yasaspeiris/WKnight-SLRC2018/Parts/midgear.STL

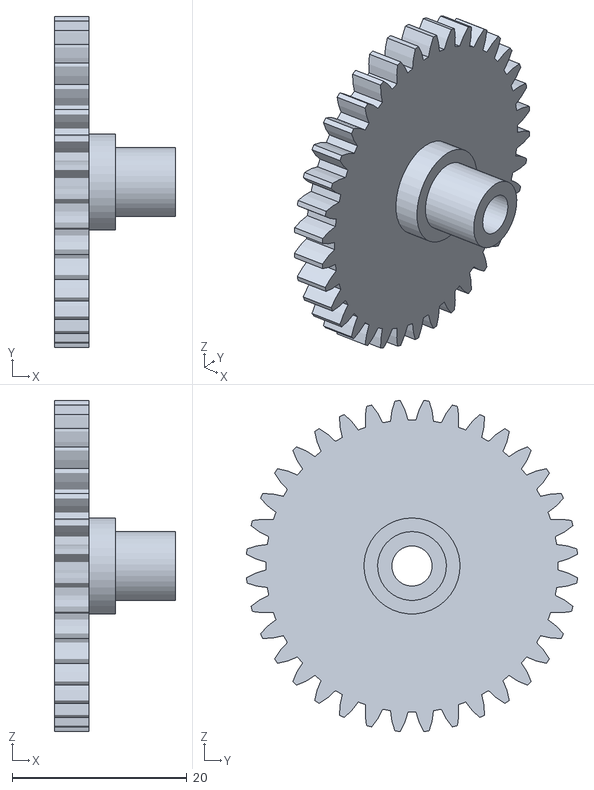
[picture p16: CAD file, 2019-01-25]
Parts/midgear.STL
13.9 x 37.9 x 37.9
