yasaspeiris/WKnight-SLRC2018/Parts/rack1.STL

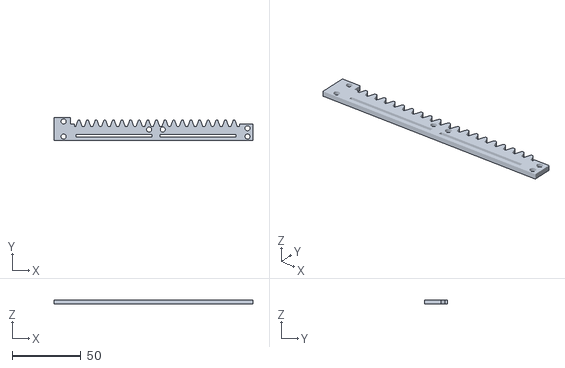
[picture p17: CAD file, 2019-01-25]
Parts/rack1.STL
145.0 x 17.0 x 3.00
