yasaspeiris/WKnight-SLRC2018/Parts/batterymount.STL

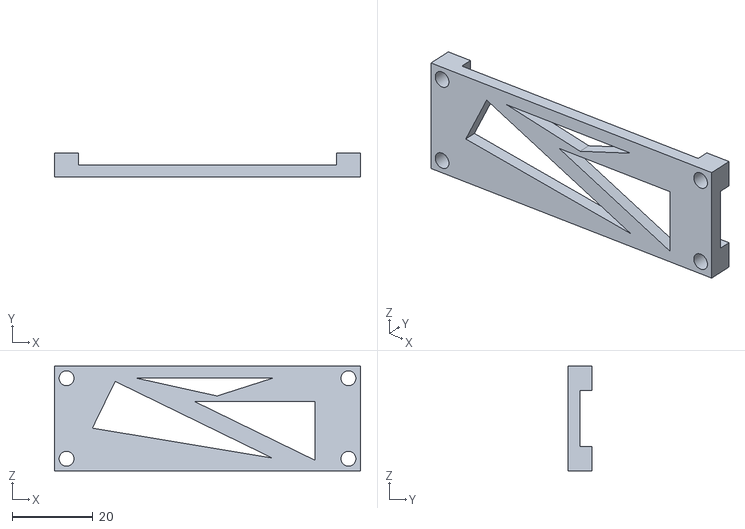
[picture p18: CAD file, 2019-01-25]
Parts/batterymount.STL
76.0 x 6.00 x 26.0
