yasaspeiris/WKnight-SLRC2018/Parts/bearingspacer_new_2.STL

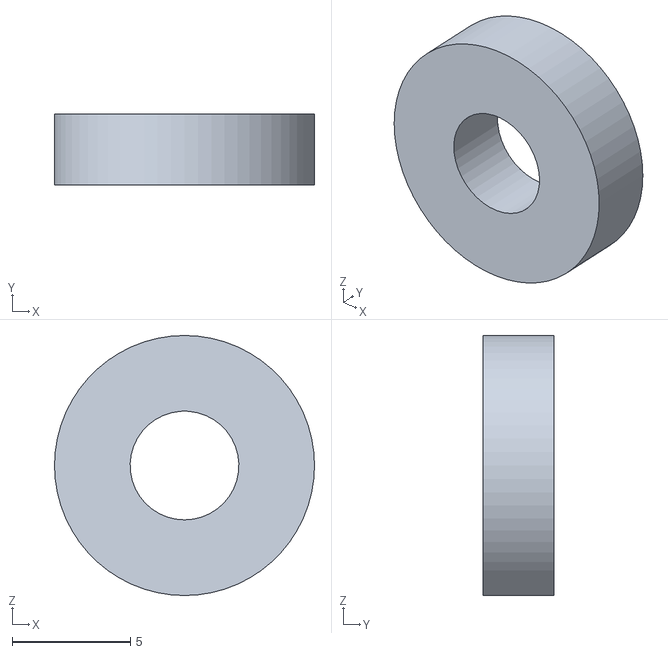
[picture p19: CAD file, 2019-01-25]
Parts/bearingspacer_new_2.STL
11.0 x 3.00 x 11.0
