yasaspeiris/WKnight-SLRC2018/Parts/trayeject.STL

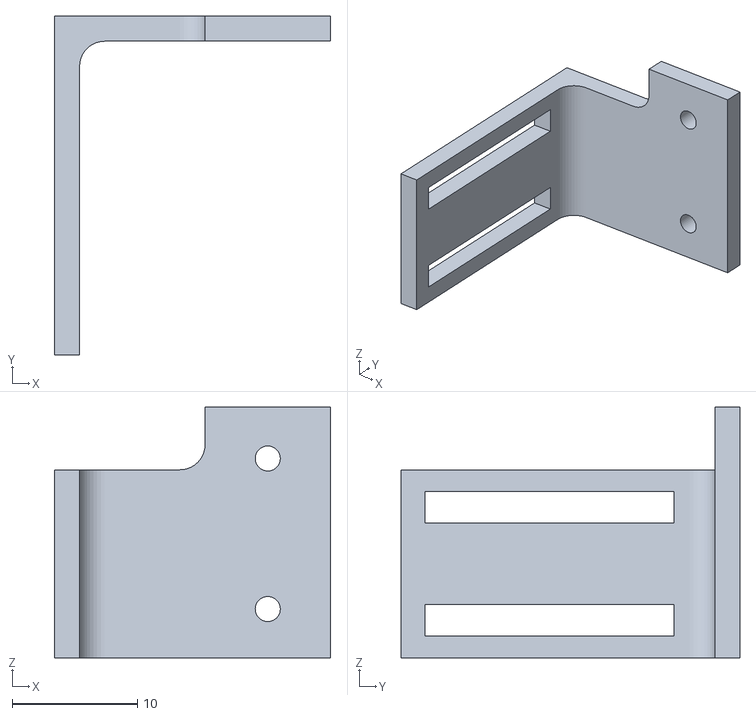
[picture p20: CAD file, 2019-01-25]
Parts/trayeject.STL
22.0 x 27.0 x 20.0
