yasaspeiris/WKnight-SLRC2018/Parts/wheelgear.STL

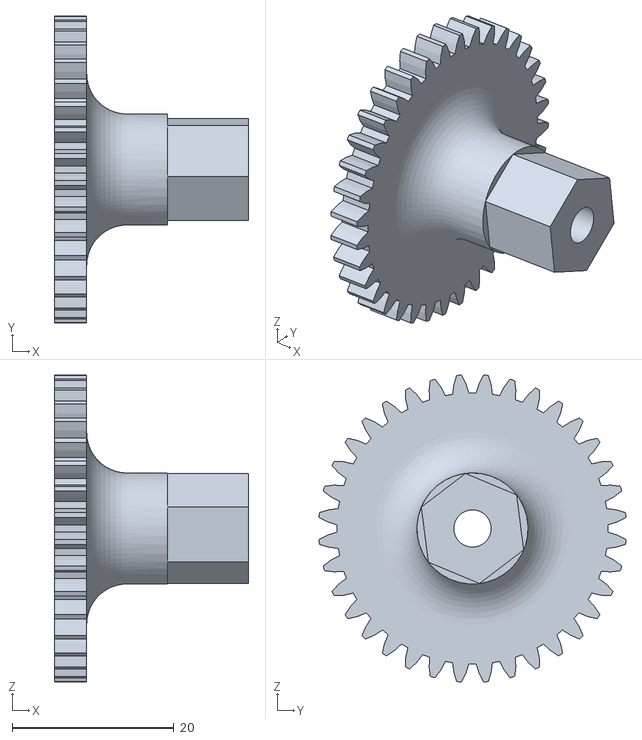
[picture p21: CAD file, 2019-01-25]
Parts/wheelgear.STL
24.0 x 37.9 x 37.9
