yasaspeiris/WKnight-SLRC2018/Parts/rightsidewall.STL

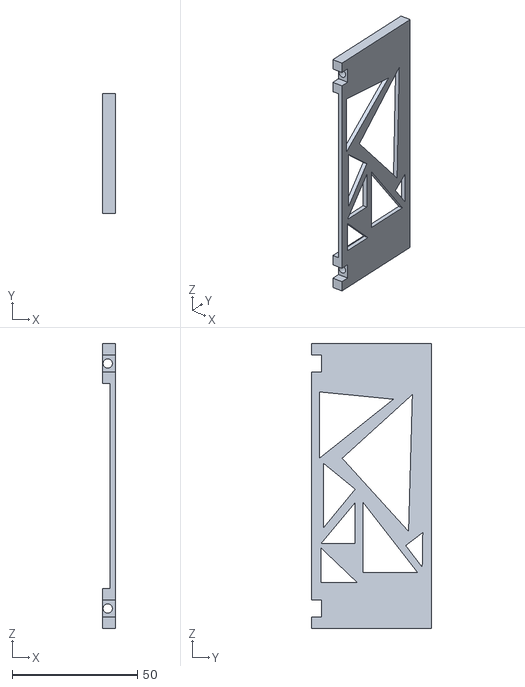
[picture p22: CAD file, 2019-01-25]
Parts/rightsidewall.STL
5.00 x 48.0 x 114.0
