yasaspeiris/WKnight-SLRC2018/Parts/experimental_motorgear.STL

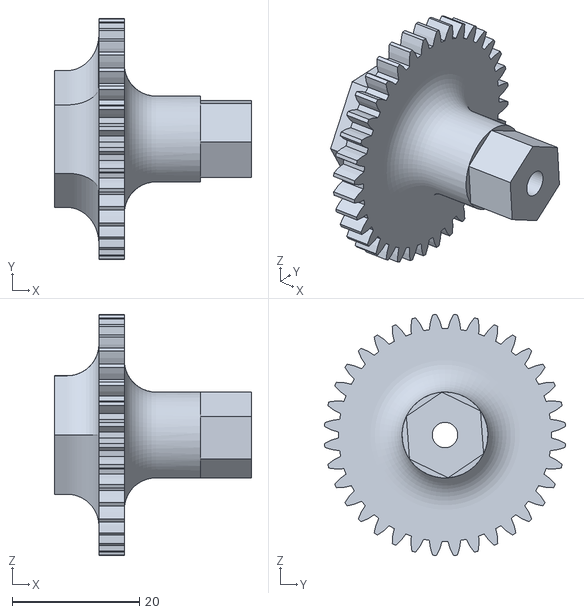
[picture p23: CAD file, 2019-01-25]
Parts/experimental_motorgear.STL
31.0 x 37.9 x 37.9
