yasaspeiris/WKnight-SLRC2018/Parts/base_top1-newnew.STL

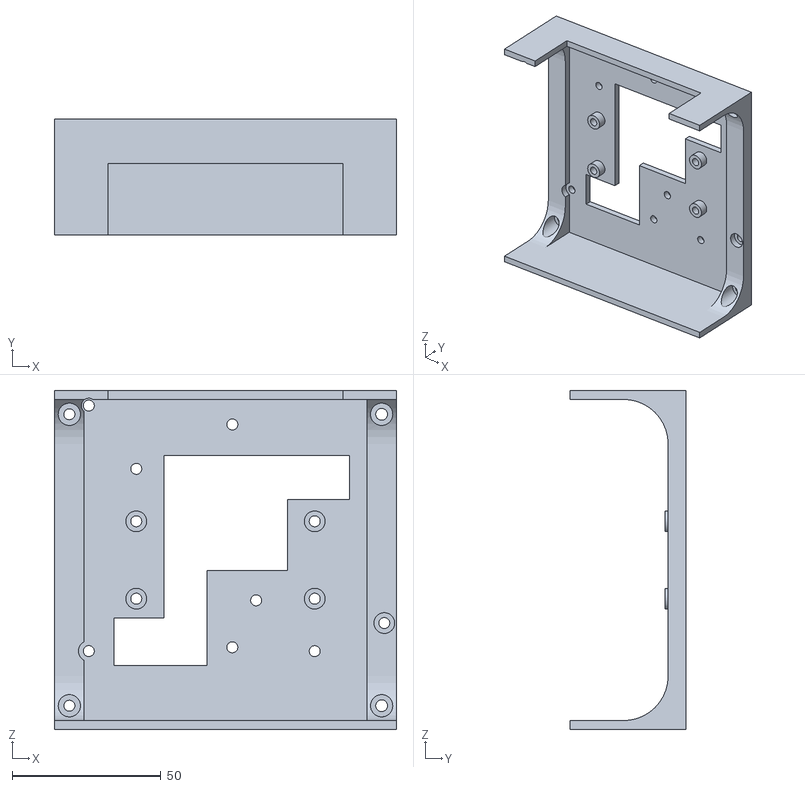
[picture p24: CAD file, 2019-01-25]
Parts/base_top1-newnew.STL
115.0 x 39.0 x 114.0
