yasaspeiris/WKnight-SLRC2018/Parts/coinremover.STL

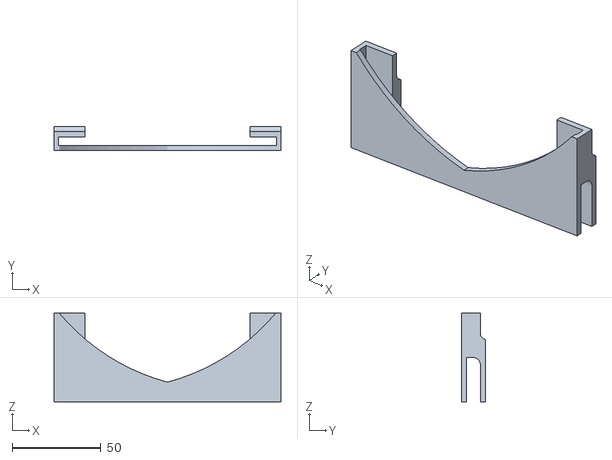
[picture p25: CAD file, 2019-01-25]
Parts/coinremover.STL
128.0 x 13.7 x 50.0
