yasaspeiris/WKnight-SLRC2018/Parts/qtrcholder_sub.STL

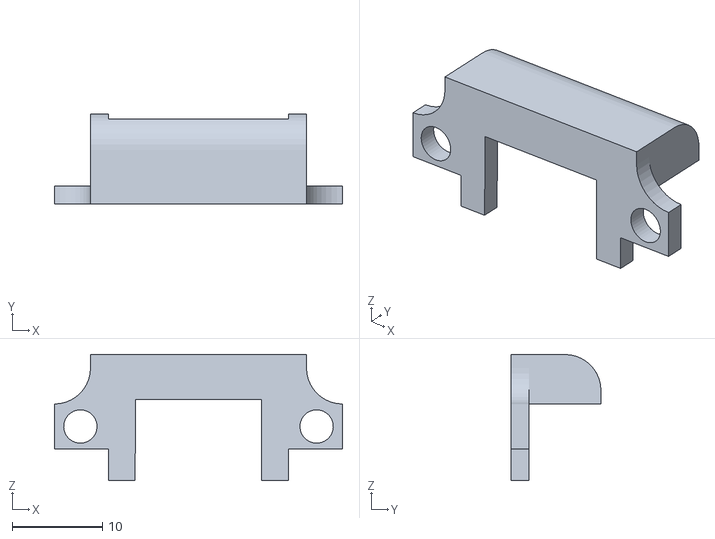
[picture p26: CAD file, 2019-01-25]
Parts/qtrcholder_sub.STL
32.0 x 10.0 x 14.0
