yasaspeiris/WKnight-SLRC2018/Parts/spurgear.STL

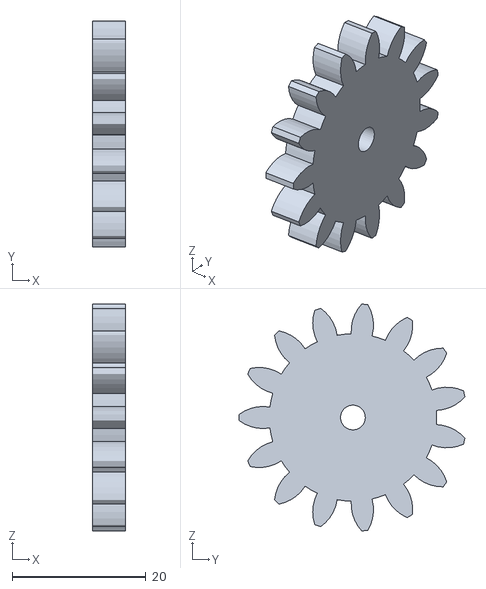
[picture p27: CAD file, 2019-01-25]
Parts/spurgear.STL
5.00 x 33.7 x 33.9
