yasaspeiris/WKnight-SLRC2018/Parts/base.STL

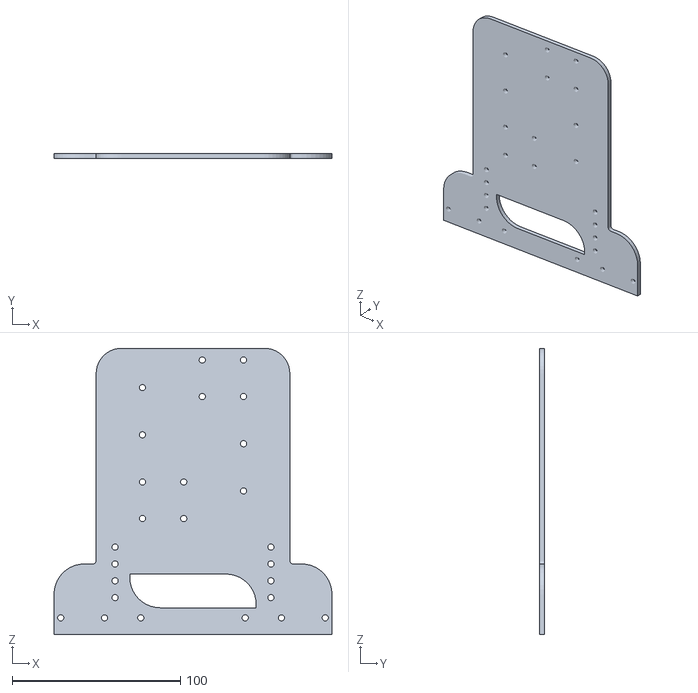
[picture p28: CAD file, 2019-01-25]
Parts/base.STL
165.0 x 3.00 x 170.0
