yasaspeiris/WKnight-SLRC2018/Parts/compartment.STL

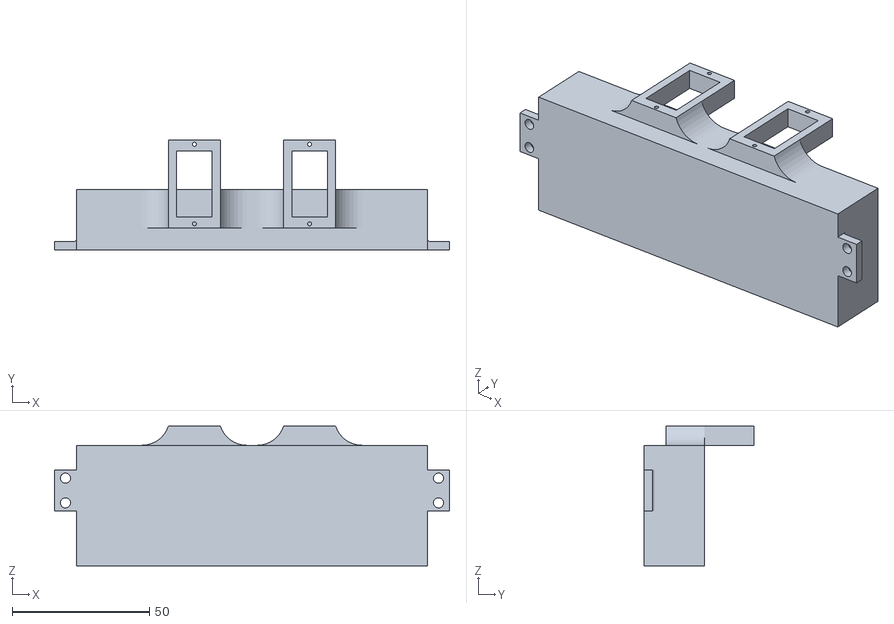
[picture p29: CAD file, 2019-01-25]
Parts/compartment.STL
144.0 x 40.0 x 51.0
