yasaspeiris/WKnight-SLRC2018/Parts/compcover1.STL

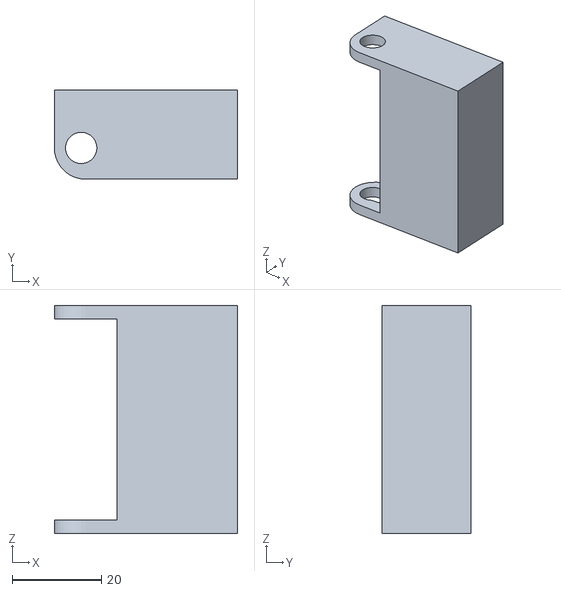
[picture p30: CAD file, 2019-01-25]
Parts/compcover1.STL
41.0 x 20.0 x 51.0
