yasaspeiris/WKnight-SLRC2018/Parts/spurgear2.STL

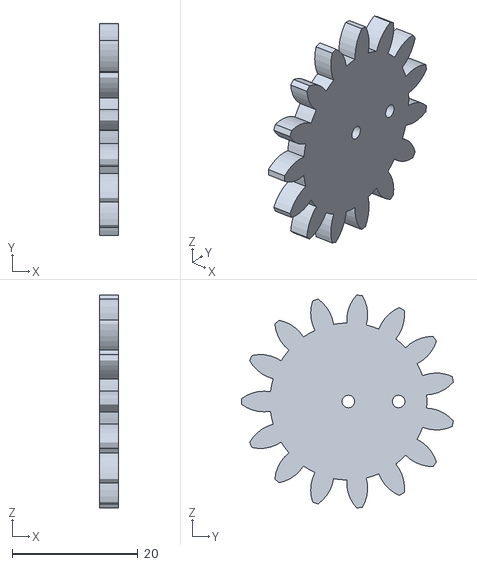
[picture p31: CAD file, 2019-01-25]
Parts/spurgear2.STL
3.00 x 33.7 x 33.9
