yasaspeiris/WKnight-SLRC2018/Parts/spacer.STL

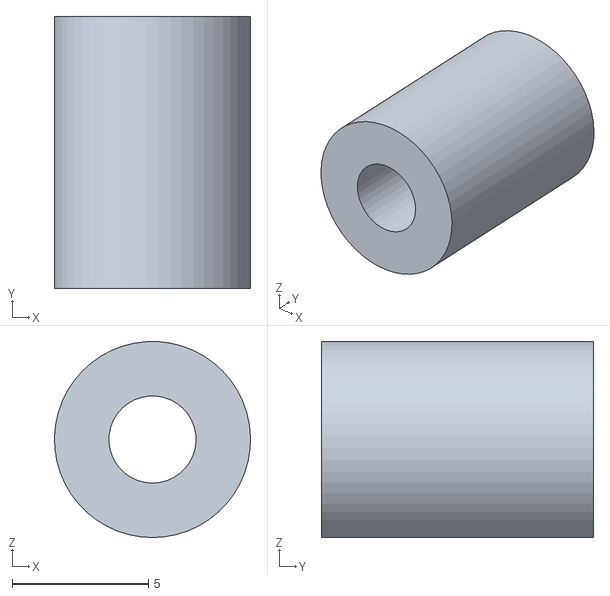
[picture p32: CAD file, 2019-01-25]
Parts/spacer.STL
7.20 x 10.0 x 7.20
