yasaspeiris/WKnight-SLRC2018/SLRC2019/lightsandsw.ino

void lightsandswsetup() {
  pinMode(STARTSWITCH, INPUT);
  pinMode(MODESW, INPUT);
  pinMode(CALSW,INPUT);
  pinMode(GREENLED,OUTPUT);
  pinMode(BLUELED, OUTPUT);
  pinMode(YELLOWLED, OUTPUT);
  

  
}
